Deadeye5589/BeoMasterAssets/DSP Source/Export/TwoWay_IC_2.h

/*
 * File:           C:\Users\Succubus\Documents\KiCad\B&O Master\DSP Source\Export\TwoWay_IC_2.h
 *
 * Created:        Thursday, December 28, 2023 4:48:27 PM
 * Description:    TwoWay:IC 2 program data.
 *
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
 * This software may only be used to program products purchased from
 * Analog Devices for incorporation by you into audio products that
 * are intended for resale to audio product end users. This software
 * may not be distributed whole or in any part to third parties.
 *
 * Copyright ©2023 Analog Devices, Inc. All rights reserved.
 */
#ifndef __TWOWAY_IC_2_H__
#define __TWOWAY_IC_2_H__

#include "SigmaStudioFW.h"
#include "TwoWay_IC_2_REG.h"

#define DEVICE_ARCHITECTURE_IC_2                  "ADAU1701"
#define DEVICE_ADDR_IC_2                          0x68

/* DSP Program Data */
#define PROGRAM_SIZE_IC_2 5120
#define PROGRAM_ADDR_IC_2 1024
ADI_REG_TYPE Program_Data_IC_2[PROGRAM_SIZE_IC_2] = {
0x00, 0x00, 0x00, 0x00, 0x01, 
0x00, 0x00, 0x00, 0xE8, 0x01, 
0x00, 0x00, 0x00, 0x00, 0x01, 
0x00, 0x08, 0x00, 0xE8, 0x01, 
0x00, 0x00, 0x00, 0x00, 0x01, 
0x00, 0x10, 0x00, 0xE8, 0x01, 
0x00, 0x00, 0x00, 0x00, 0x01, 
0x00, 0x18, 0x00, 0xE8, 0x01, 
0xFF, 0xF2, 0x00, 0x20, 0x01, 
0x00, 0x58, 0x00, 0xE2, 0x01, 
0x00, 0x01, 0x08, 0x20, 0x01, 
0x00, 0x30, 0x00, 0xE2, 0x01, 
0x00, 0x09, 0x08, 0x20, 0x01, 
0x00, 0x40, 0x00, 0xE2, 0x01, 
0x00, 0x11, 0x08, 0x20, 0x01, 
0x00, 0x38, 0x00, 0xE2, 0x01, 
0x00, 0x19, 0x08, 0x20, 0x01, 
0x00, 0x48, 0x00, 0xE2, 0x01, 
0xFF, 0xE9, 0x08, 0x20, 0x01, 
0x00, 0xB0, 0x00, 0xE2, 0x01, 
0x00, 0x51, 0x08, 0x20, 0x01, 
0x00, 0x59, 0x08, 0x22, 0x49, 
0xFF, 0xF1, 0x08, 0x20, 0x26, 
0x00, 0xB0, 0x00, 0xE2, 0x01, 
0x00, 0x71, 0x08, 0x20, 0x01, 
0xFF, 0xF1, 0x13, 0x22, 0x49, 
0x00, 0x51, 0x08, 0x20, 0x01, 
0x00, 0x91, 0x08, 0x20, 0x25, 
0x00, 0x98, 0x00, 0xE2, 0x01, 
0x00, 0x81, 0x08, 0x20, 0x01, 
0xFF, 0xF1, 0x13, 0x22, 0x49, 
0x00, 0x51, 0x08, 0x20, 0x01, 
0x00, 0xA1, 0x08, 0x20, 0x25, 
0x00, 0xA8, 0x00, 0xE2, 0x01, 
0x00, 0xB9, 0x08, 0x20, 0x01, 
0x00, 0x00, 0x00, 0x00, 0x01, 
0x00, 0xC8, 0x00, 0xF0, 0x01, 
0x00, 0xC9, 0x08, 0x20, 0x01, 
0xFF, 0xF1, 0x13, 0x22, 0x49, 
0x00, 0xB1, 0x08, 0x20, 0x01, 
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
};

/* DSP Parameter (Coefficient) Data */
#define PARAM_SIZE_IC_2 4096
#define PARAM_ADDR_IC_2 0
ADI_REG_TYPE Param_Data_IC_2[PARAM_SIZE_IC_2] = {
0x00, 0x00, 0x00, 0x01, 
0x00, 0x80, 0x00, 0x00, 
0x00, 0x80, 0x00, 0x00, 
0x00, 0x00, 0x4E, 0xB0, 
0x00, 0x00, 0x01, 0xE0, 
0x00, 0x00, 0x07, 0x1C, 
0x00, 0x00, 0x4E, 0xB0, 
0x00, 0x00, 0x01, 0xE0, 
0x00, 0x00, 0x07, 0x1C, 
0x00, 0x00, 0x0F, 0xB9, 
0x00, 0x00, 0x03, 0x8E, 
0x00, 0x00, 0x01, 0x54, 
0x00, 0x00, 0x02, 0xA8, 
0x00, 0x00, 0x01, 0x54, 
0x00, 0xFD, 0xF3, 0x4B, 
0x0F, 0x82, 0x07, 0x65, 
0x00, 0x02, 0xC6, 0x9C, 
0x0F, 0xFD, 0x78, 0xB3, 
0x0F, 0xFF, 0xC1, 0x1B, 
0x00, 0xFC, 0xDA, 0x44, 
0x0F, 0x82, 0xFC, 0xA7, 
0x00, 0x04, 0x3C, 0xCF, 
0x0F, 0xFD, 0x81, 0x62, 
0x0F, 0xFE, 0x43, 0x6E, 
0x00, 0xF9, 0x75, 0xBD, 
0x0F, 0x85, 0xE7, 0xE0, 
0x00, 0x07, 0x10, 0x98, 
0x0F, 0xFD, 0x94, 0x8D, 
0x0F, 0xFB, 0x61, 0x32, 
0x00, 0xF1, 0xF8, 0xC3, 
0x0F, 0x8B, 0x8D, 0x28, 
0x00, 0x0E, 0xDF, 0x92, 
0x0F, 0xFD, 0xDA, 0xE7, 
0x0F, 0xF3, 0x6A, 0x4D, 
0x00, 0xD6, 0x7D, 0xD0, 
0x0F, 0x9B, 0x24, 0xCE, 
0x00, 0x1A, 0x25, 0x7A, 
0x0F, 0xFE, 0x70, 0x38, 
0x0F, 0xE7, 0xEA, 0xC5, 
0x00, 0x9C, 0x2A, 0x09, 
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
};


/* Register Default - IC 2.CoreRegister */
ADI_REG_TYPE R0_COREREGISTER_IC_2_Default[REG_COREREGISTER_IC_2_BYTE] = {
0x00, 0x18
};

/* Register Default - IC 2.HWConFiguration */
#define R3_HWCONFIGURATION_IC_2_SIZE 24
ADI_REG_TYPE R3_HWCONFIGURATION_IC_2_Default[R3_HWCONFIGURATION_IC_2_SIZE] = {
0x00, 0x18, 0x08, 0x08, 0x02, 0x00, 0x44, 0x44, 0x44, 0x44, 0x44, 0x44, 0x00, 0x00, 0x00, 0x00, 0x80, 0x00, 0x00, 0x00, 0x00, 0x00, 0x00, 0x01
};

/* Register Default - IC 2.CoreRegister */
ADI_REG_TYPE R4_COREREGISTER_IC_2_Default[REG_COREREGISTER_IC_2_BYTE] = {
0x00, 0x1C
};


/*
 * Default Download
 */
#define DEFAULT_DOWNLOAD_SIZE_IC_2 5

void default_download_IC_2() {
	SIGMA_WRITE_REGISTER_BLOCK( DEVICE_ADDR_IC_2, REG_COREREGISTER_IC_2_ADDR, REG_COREREGISTER_IC_2_BYTE, R0_COREREGISTER_IC_2_Default );
	SIGMA_WRITE_REGISTER_BLOCK( DEVICE_ADDR_IC_2, PROGRAM_ADDR_IC_2, PROGRAM_SIZE_IC_2, Program_Data_IC_2 );
	SIGMA_WRITE_REGISTER_BLOCK( DEVICE_ADDR_IC_2, PARAM_ADDR_IC_2, PARAM_SIZE_IC_2, Param_Data_IC_2 );
	SIGMA_WRITE_REGISTER_BLOCK( DEVICE_ADDR_IC_2, REG_COREREGISTER_IC_2_ADDR , R3_HWCONFIGURATION_IC_2_SIZE, R3_HWCONFIGURATION_IC_2_Default );
	SIGMA_WRITE_REGISTER_BLOCK( DEVICE_ADDR_IC_2, REG_COREREGISTER_IC_2_ADDR, REG_COREREGISTER_IC_2_BYTE, R4_COREREGISTER_IC_2_Default );
}

#endif
